nullboundary/Triggertrap/Board Schematics/TT Shield for Arduino schematics v39/TriggerTrap Shield 0v24 Release.sch.png

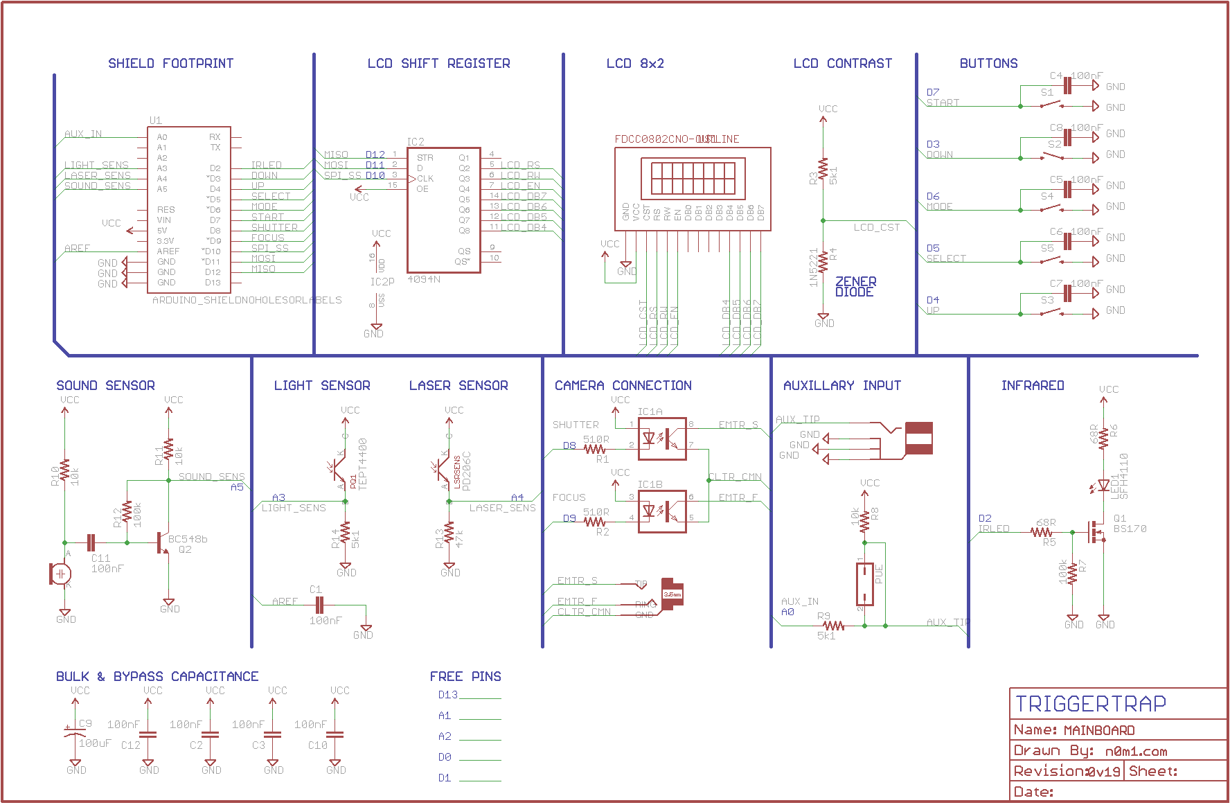
Board Schematics/TT Shield for Arduino schematics v39/TriggerTrap Shield 0v24 Release.sch.png
